open-seneca/modular-aq-sensor/casing/Laser_cut_makespace/top.dxf

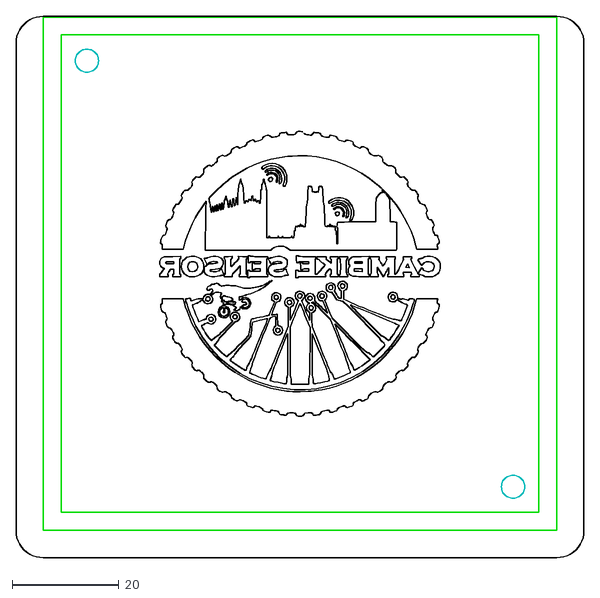
[picture p36: CAD file, 2018-09-05]
casing/Laser_cut_makespace/top.dxf
106.7 x 101.7
