open-seneca/modular-aq-sensor/casing/Laser_cut_makespace/cover.dxf

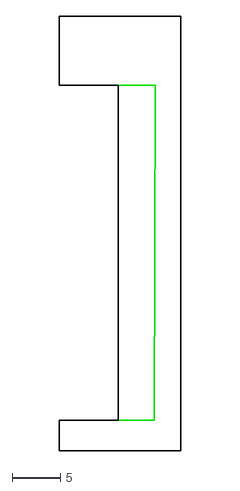
[picture p37: CAD file, 2018-09-05]
casing/Laser_cut_makespace/cover.dxf
12.7 x 45.1
