open-seneca/modular-aq-sensor/casing/Laser_cut_makespace/sd_card_side.dxf

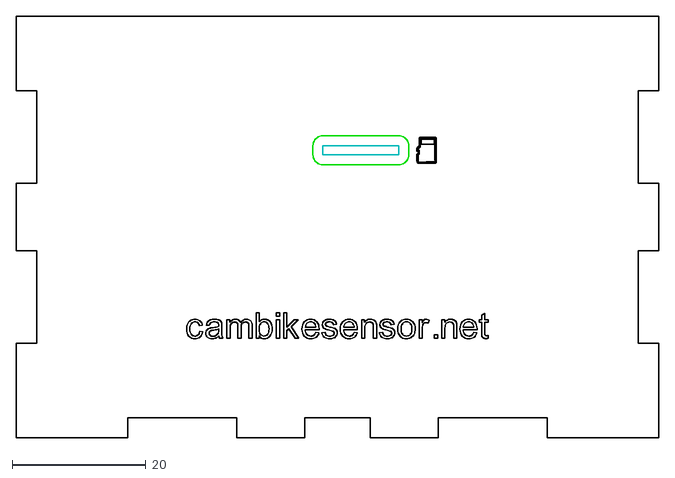
[picture p38: CAD file, 2018-09-05]
casing/Laser_cut_makespace/sd_card_side.dxf
96.1 x 63.1
