open-seneca/modular-aq-sensor/casing/Laser_cut_makespace/base.dxf

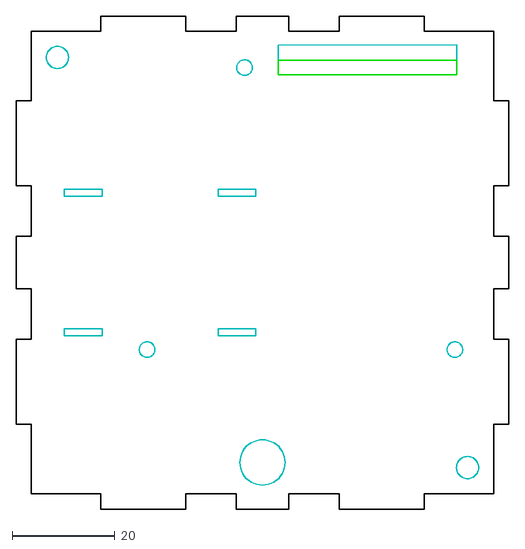
[picture p39: CAD file, 2018-09-05]
casing/Laser_cut_makespace/base.dxf
96.1 x 96.1
